skiselev/xt-cf-lite-v4/KiCad/xt-cf.sch

## KiCad design KiCad/xt-cf.sch (2023-10-31)

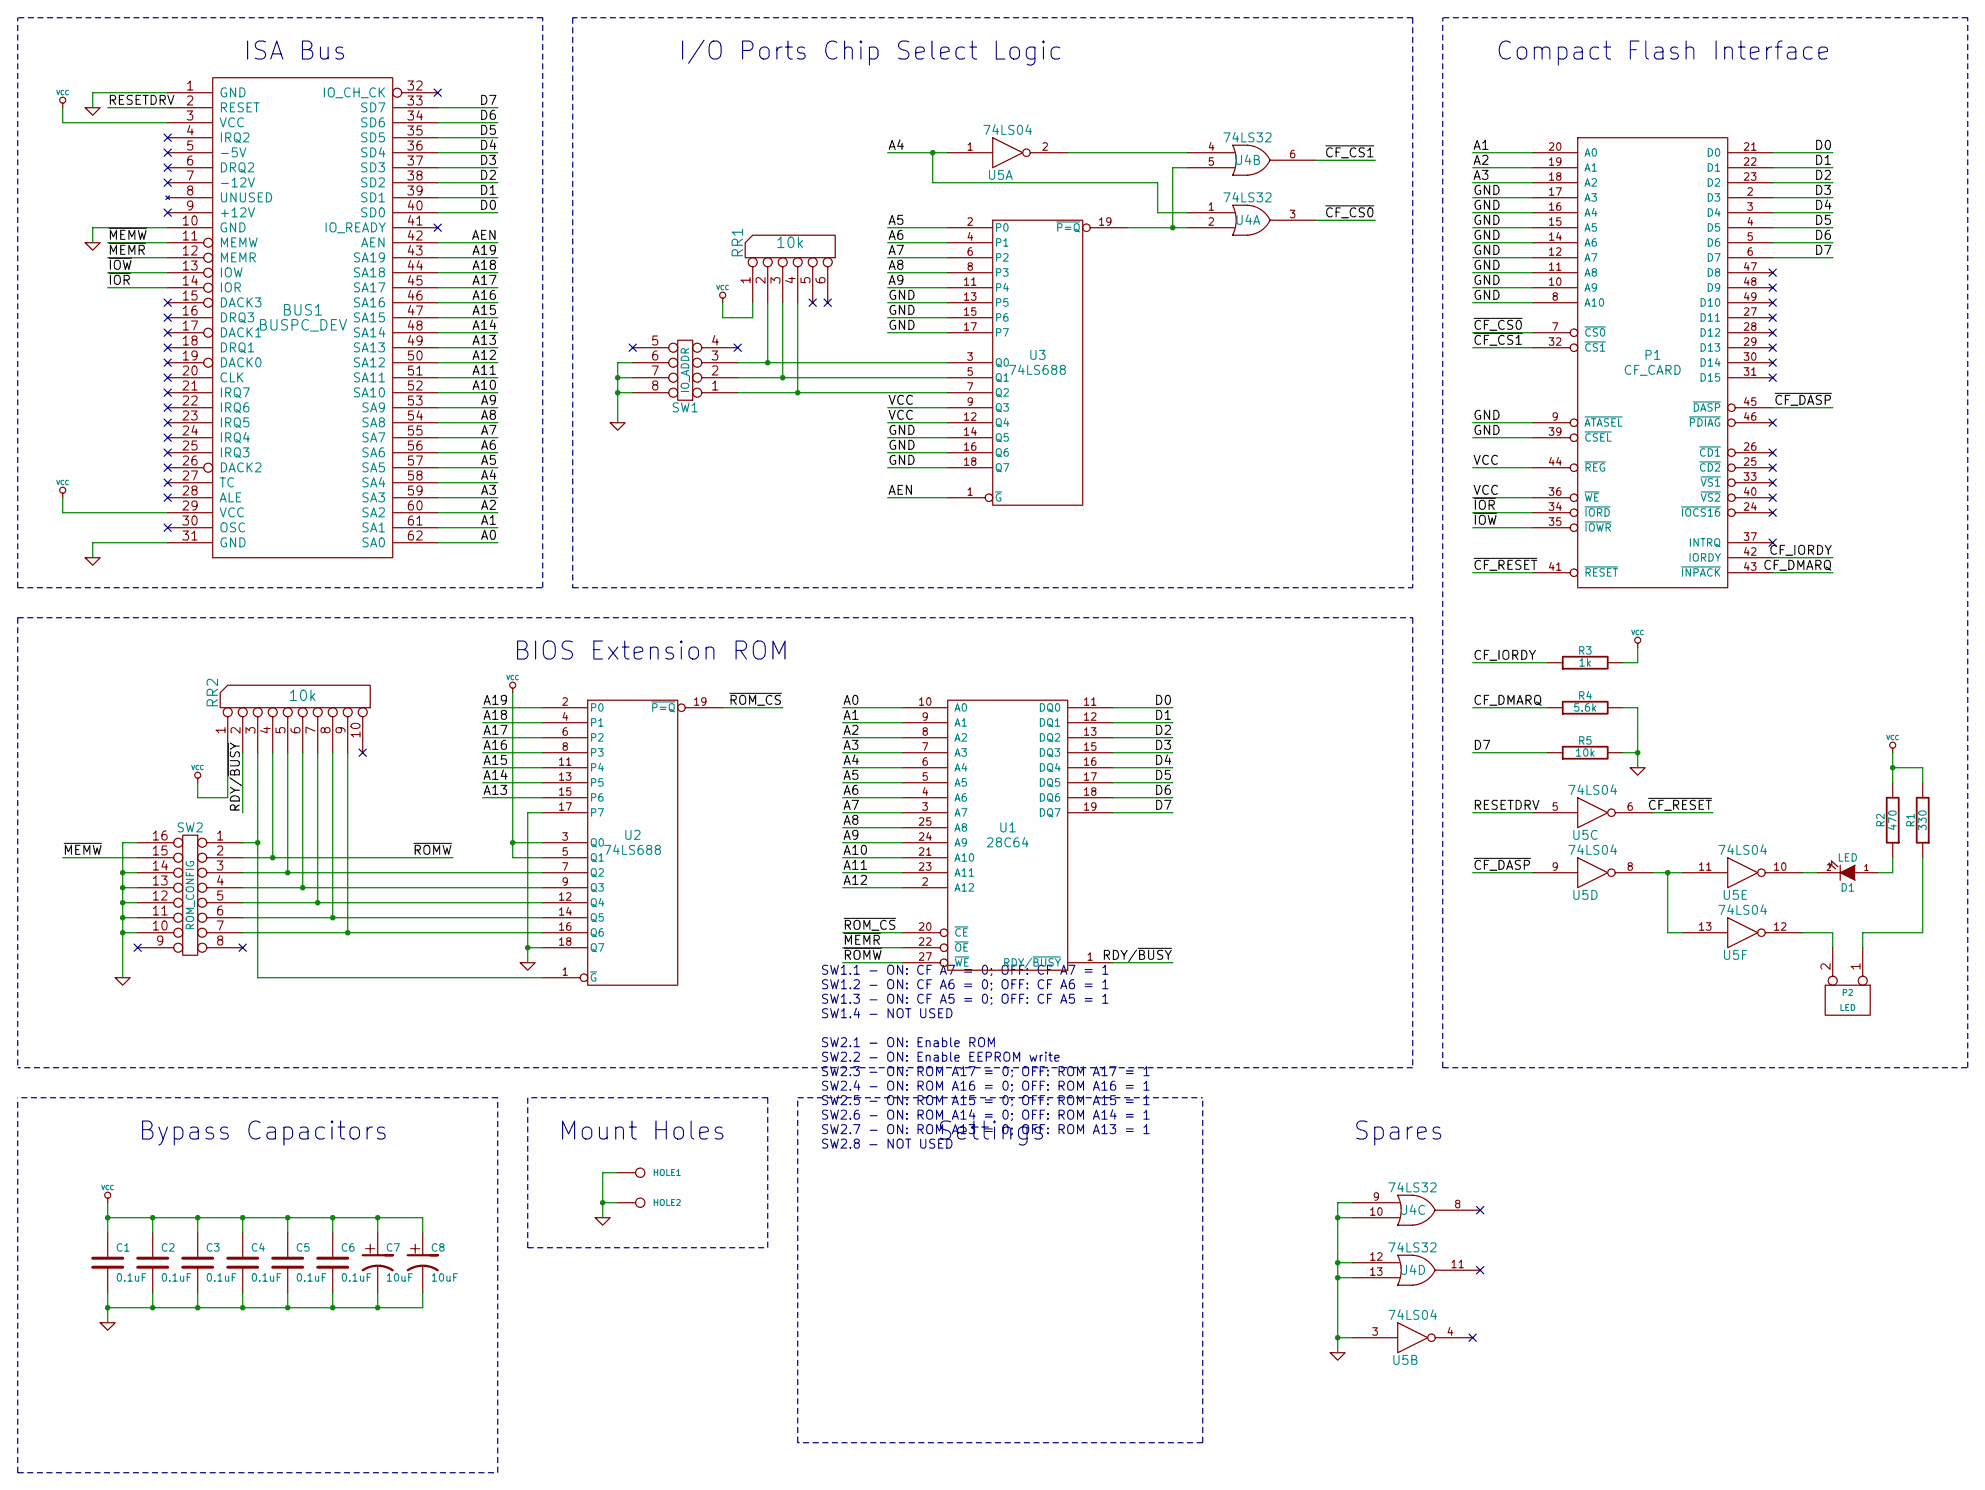
[picture p9: schematic xt-cf.sch]

Parts:
BUS1: BUSPC_DEV
C1, C2, C3, C4, C5, C6: 0.1uF
C7, C8: 10uF
D1: LED
HOLE1, HOLE2: CONN_1
P1: CF_CARD
P2: LED
R1: 330
R2: 470
R3: 1k
R4: 5.6k
R5: 10k
RR1, RR2: 10k
SW1: IO_ADDR
SW2: ROM_CONFIG
U1: 28C64
U2, U3: 74LS688
U4: 74LS32
U5: 74LS04

Connections:
A0: BUS1.62 (SA0), U1.10 (A0)
A1: BUS1.61 (SA1), P1.20 (A0), U1.9 (A1)
A2: BUS1.60 (SA2), P1.19 (A1), U1.8 (A2)
A3: BUS1.59 (SA3), P1.18 (A2), U1.7 (A3)
A4: BUS1.58 (SA4), U1.6 (A4), U4.1, U5.1
A5: BUS1.57 (SA5), U1.5 (A5), U3.2 (P0)
A6: BUS1.56 (SA6), U1.4 (A6), U3.4 (P1)
A7: BUS1.55 (SA7), U1.3 (A7), U3.6 (P2)
A8: BUS1.54 (SA8), U1.25 (A8), U3.8 (P3)
A9: BUS1.53 (SA9), U1.24 (A9), U3.11 (P4)
A10: BUS1.52 (SA10), U1.21 (A10)
A11: BUS1.51 (SA11), U1.23 (A11)
A12: BUS1.50 (SA12), U1.2 (A12)
A13: BUS1.49 (SA13), U2.15 (P6)
A14: BUS1.48 (SA14), U2.13 (P5)
A15: BUS1.47 (SA15), U2.11 (P4)
A16: BUS1.46 (SA16), U2.8 (P3)
A17: BUS1.45 (SA17), U2.6 (P2)
A18: BUS1.44 (SA18), U2.4 (P1)
A19: BUS1.43 (SA19), U2.2 (P0)
AEN: BUS1.42 (AEN), U3.1 (~G)
CF_DMARQ: P1.43 (~INPACK), R4.1
CF_IORDY: P1.42 (IORDY), R3.1
D0: BUS1.40 (SD0), P1.21 (D0), U1.11 (DQ0)
D1: BUS1.39 (SD1), P1.22 (D1), U1.12 (DQ1)
D2: BUS1.38 (SD2), P1.23 (D2), U1.13 (DQ2)
D3: BUS1.37 (SD3), P1.2 (D3), U1.15 (DQ3)
D4: BUS1.36 (SD4), P1.3 (D4), U1.16 (DQ4)
D5: BUS1.35 (SD5), P1.4 (D5), U1.17 (DQ5)
D6: BUS1.34 (SD6), P1.5 (D6), U1.18 (DQ6)
D7: BUS1.33 (SD7), P1.6 (D7), R5.1, U1.19 (DQ7)
GND: BUS1.1 (GND), BUS1.10 (GND), BUS1.31 (GND), C1.2, C2.2, C3.2, C4.2, C5.2, C6.2, C7.2, C8.2, HOLE1.1, HOLE2.1, P1.8 (A10), P1.9 (~ATASEL), P1.10 (A9), P1.11 (A8), P1.12 (A7), P1.14 (A6), P1.15 (A5), P1.16 (A4), P1.17 (A3), P1.39 (~CSEL), R4.2, R5.2, SW1.6, SW1.7, SW1.8, SW2.10, SW2.11, SW2.12, SW2.13, SW2.14, SW2.16, U2.17 (P7), U2.18 (Q7), U3.13 (P5), U3.14 (Q5), U3.15 (P6), U3.16 (Q6), U3.17 (P7), U3.18 (Q7), U4.9, U4.10, U4.12, U4.13, U5.3
unnamed: D1.1 (A), R2.1
unnamed: D1.2 (K), U5.10
unnamed: P2.1, R1.1
unnamed: P2.2 (PM), U5.12
unnamed: RR1.2, SW1.3, U3.3 (Q0)
unnamed: RR1.3, SW1.2, U3.5 (Q1)
unnamed: RR1.4, SW1.1, U3.7 (Q2)
unnamed: RR2.3, SW2.1, U2.1 (~G)
unnamed: RR2.5, SW2.3, U2.7 (Q2)
unnamed: RR2.6, SW2.4, U2.9 (Q3)
unnamed: RR2.7, SW2.5, U2.12 (Q4)
unnamed: RR2.8, SW2.6, U2.14 (Q5)
unnamed: RR2.9, SW2.7, U2.16 (Q6)
unnamed: U3.19 (~P=Q), U4.2, U4.5
unnamed: U4.4, U5.2
unnamed: U5.8, U5.11, U5.13
RDY/~BUSY: RR2.2, U1.1 (RDY/~BUSY)
RESETDRV: BUS1.2 (RESET), U5.5
VCC: BUS1.3 (VCC), BUS1.29 (VCC), C1.1, C2.1, C3.1, C4.1, C5.1, C6.1, C7.1, C8.1, P1.36 (~WE), P1.44 (~REG), R1.2, R2.2, R3.2, RR1.1 (COM), RR2.1 (COM), U2.3 (Q0), U2.5 (Q1), U3.9 (Q3), U3.12 (Q4)
~CF_CS0: P1.7 (~CS0), U4.3
~CF_CS1: P1.32 (~CS1), U4.6
~CF_DASP: P1.45 (~DASP), U5.9
~CF_RESET: P1.41 (~RESET), U5.6
~IOR: BUS1.14 (IOR), P1.34 (~IORD)
~IOW: BUS1.13 (IOW), P1.35 (~IOWR)
~MEMR: BUS1.12 (MEMR), U1.22 (~OE)
~MEMW: BUS1.11 (MEMW), SW2.15
~ROMW: RR2.4, SW2.2, U1.27 (~WE)
~ROM_CS: U1.20 (~CE), U2.19 (~P=Q)

Notes on the sheet:
Spares
ISA Bus
BIOS Extension ROM
Bypass Capacitors
Mount Holes
I/O Ports Chip Select Logic
Compact Flash Interface
SW1.1 - ON: CF A7 = 0; OFF: CF A7 = 1 SW1.2 - ON: CF A6 = 0; OFF: CF A6 = 1 SW1.3 - ON: CF A5 = 0; OFF: CF A5 = 1 SW1.4 - NOT USED SW2.1 - ON: Enable ROM SW2.2 - ON: Enable EEPROM write SW2.3 - ON: ROM A17 = 0; OFF: ROM A17 = 1 SW2.4 - ON: ROM A16 = 0; OFF: ROM A16 = 1 SW2.5 - ON: ROM A15 = 0; OFF: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
Settings
